Elipsit/ext-LED-Lamps/pics/IMG_0184.jpeg

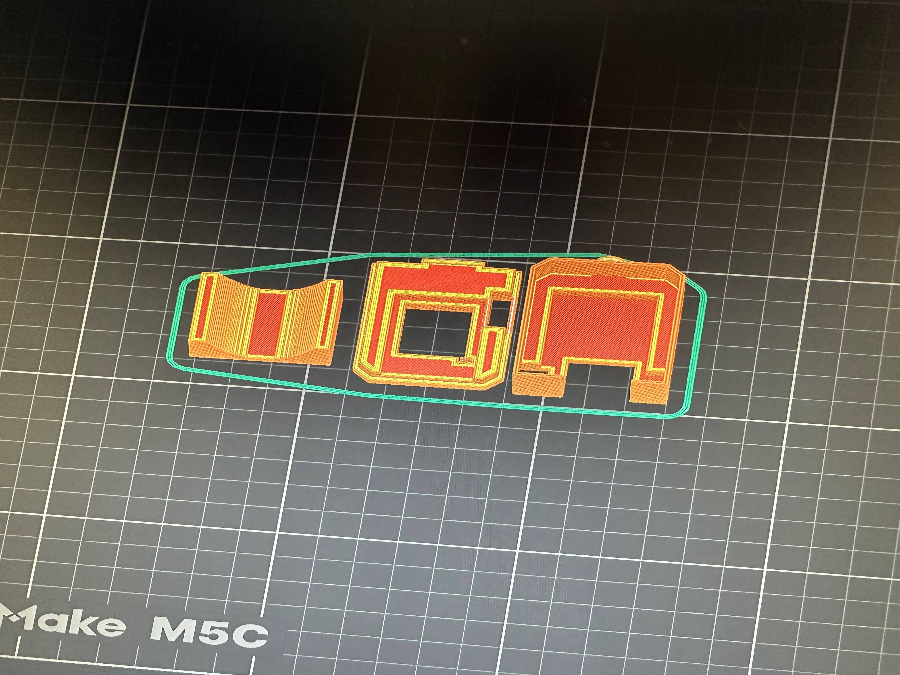
pics/IMG_0184.jpeg
