Elipsit/ext-LED-Lamps/pics/IMG_0197.jpeg

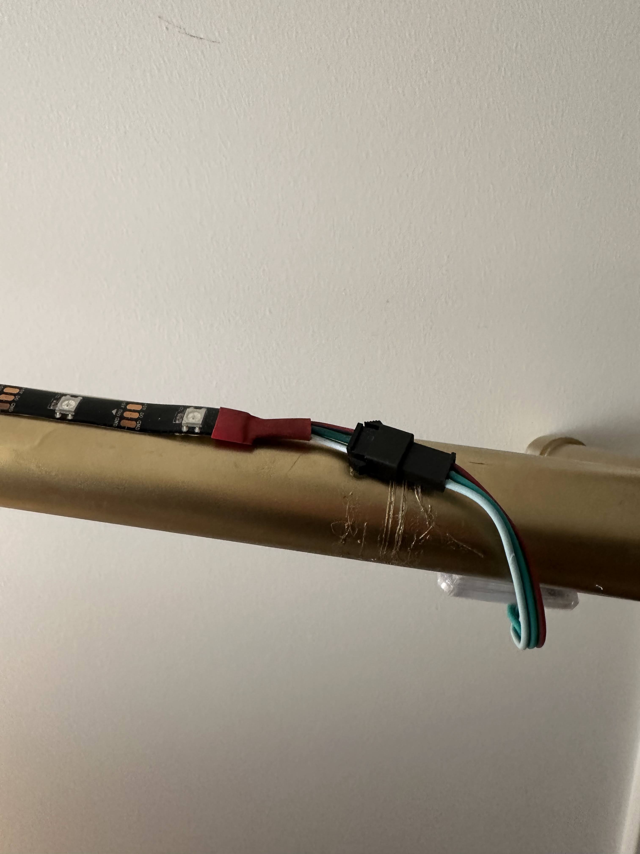
pics/IMG_0197.jpeg
