Elipsit/ext-LED-Lamps/pics/IMG_0308.jpeg

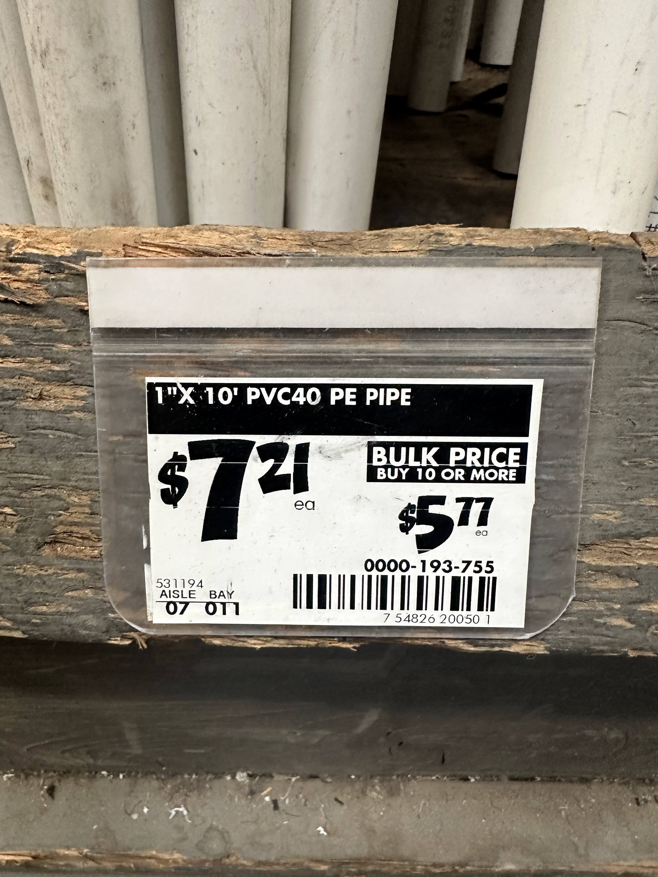
pics/IMG_0308.jpeg
