Elipsit/ext-LED-Lamps/pics/IMG_0309.jpeg

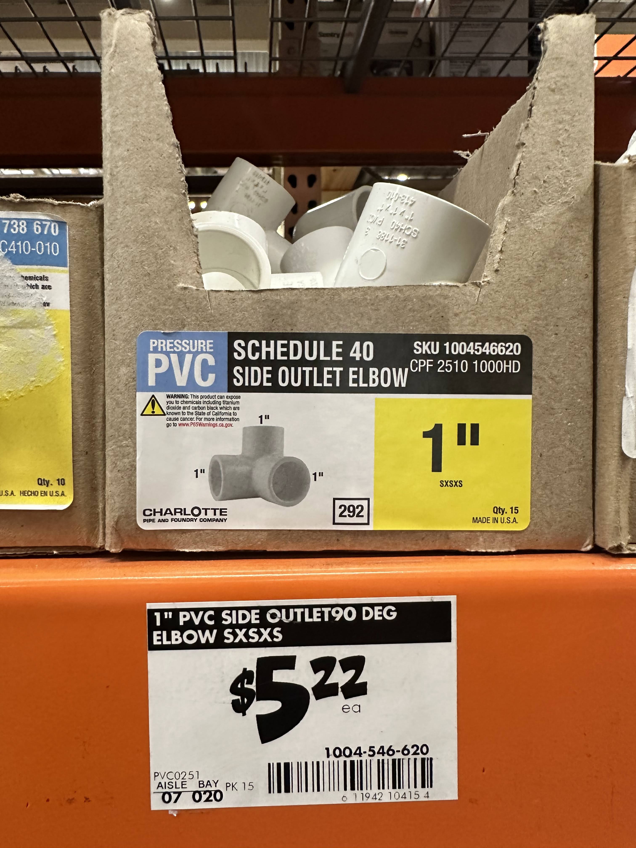
pics/IMG_0309.jpeg
