Elipsit/ext-LED-Lamps/ME/3D Print Outputs/plug-lamp v1.png

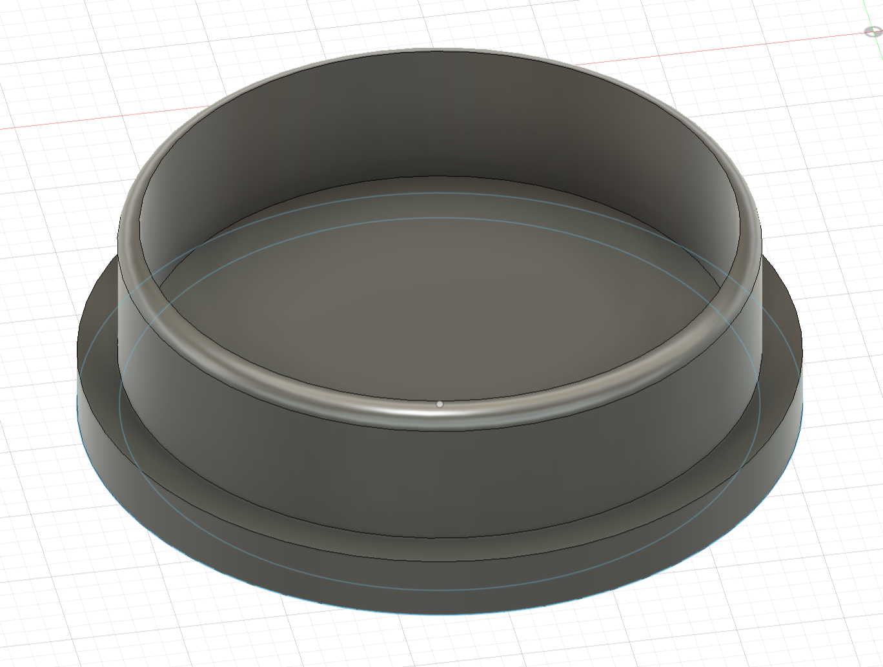
ME/3D Print Outputs/plug-lamp v1.png
